sandgum/E-ink-Smartwatch/CAD/OLED Segment/top plate (OLED).step

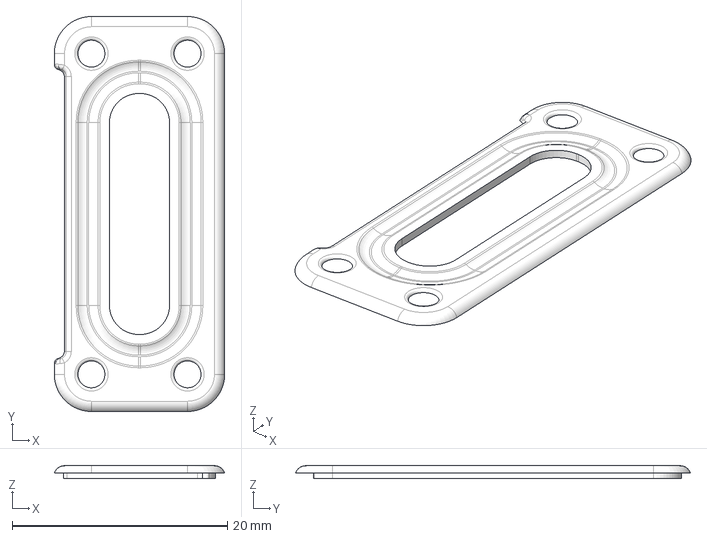
[picture p12: CAD file, 2025-12-07]
CAD/OLED Segment/top plate (OLED).step
15.8 x 36.7 x 1.17 mm
