sandgum/E-ink-Smartwatch/CAD/Components/haptic motor.step

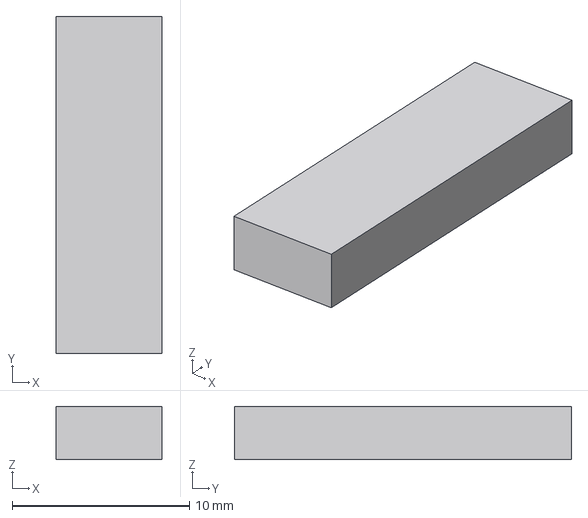
[picture p13: CAD file, 2025-12-07]
CAD/Components/haptic motor.step
6.00 x 19.0 x 3.00 mm
