sandgum/E-ink-Smartwatch/CAD/E-Ink Segment/top plate (E-ink).step

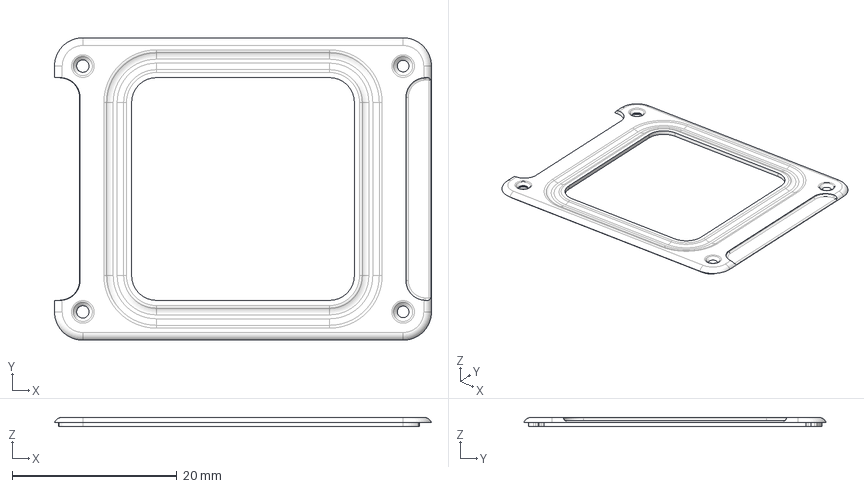
[picture p14: CAD file, 2025-12-07]
CAD/E-Ink Segment/top plate (E-ink).step
45.7 x 36.7 x 1.13 mm
