sandgum/E-ink-Smartwatch/CAD/Components/100mah battery (3).step

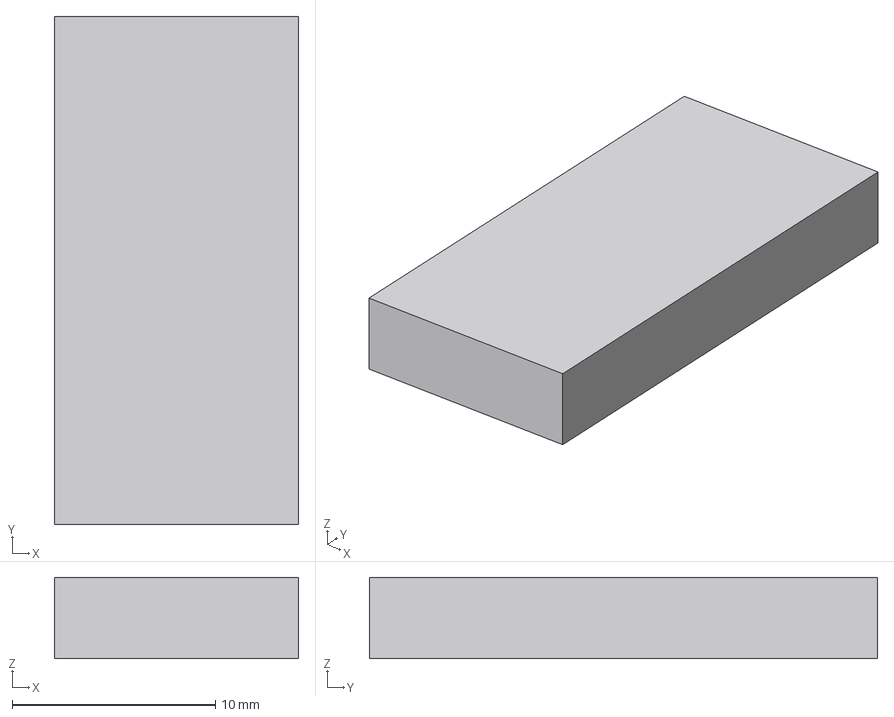
[picture p15: CAD file, 2025-12-07]
CAD/Components/100mah battery (3).step
12.0 x 25.0 x 4.00 mm
