sandgum/E-ink-Smartwatch/CAD/Components/e ink display.step

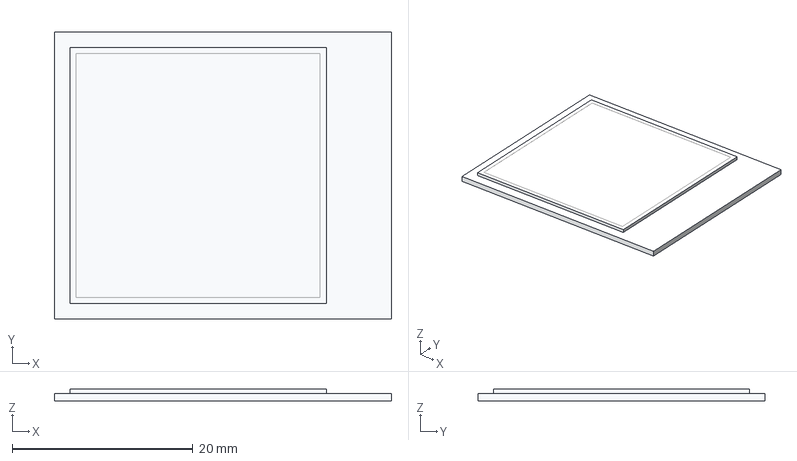
[picture p16: CAD file, 2025-12-07]
CAD/Components/e ink display.step
37.3 x 31.8 x 1.35 mm
