sandgum/E-ink-Smartwatch/CAD/Components/Button.step

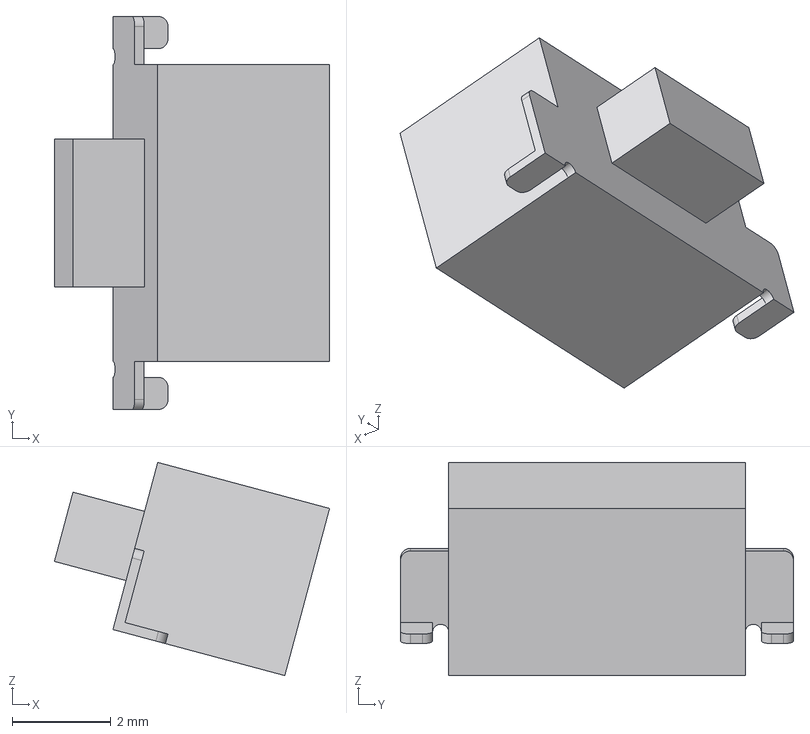
[picture p17: CAD file, 2025-12-07]
CAD/Components/Button.step
5.57 x 7.95 x 4.31 mm
